jamescoxon/LPC810/src/adc.h

// adc.h
// adapted from http://blog.nano-age.co.uk/2014_08_01_archive.html
#ifndef _ADC_H_
#define _ADC_H_

#ifdef __cplusplus
extern "C" {
#endif

#include "LPC8xx.h"

int read_adc2();
    
#ifdef __cplusplus
}
#endif

#endif
